Hans-Beerman/NodeOven/Photos/20200808_105303.jpg

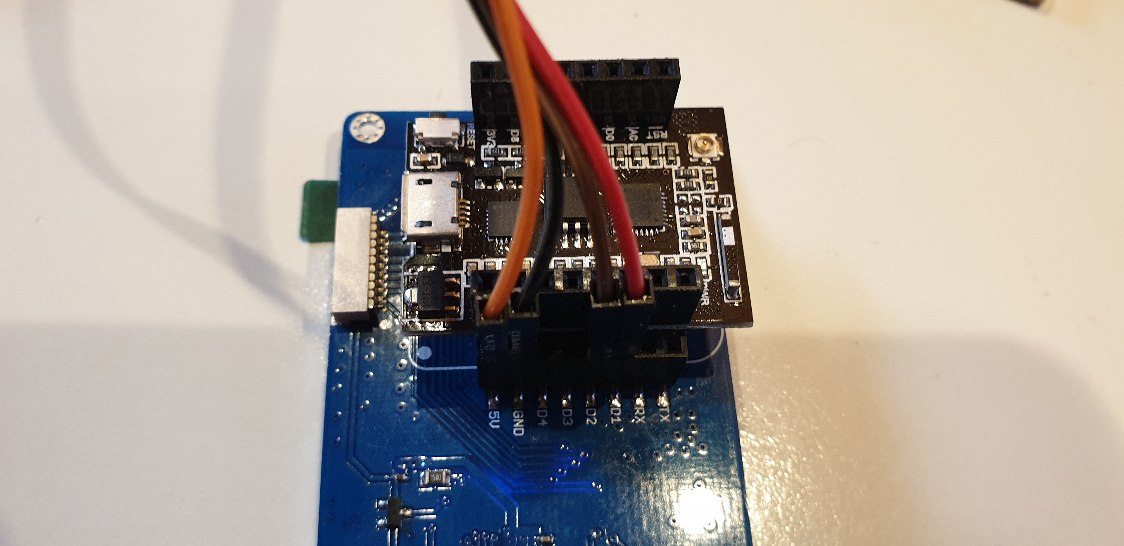
Photos/20200808_105303.jpg
