Hans-Beerman/NodeOven/Photos/20200808_163038.jpg

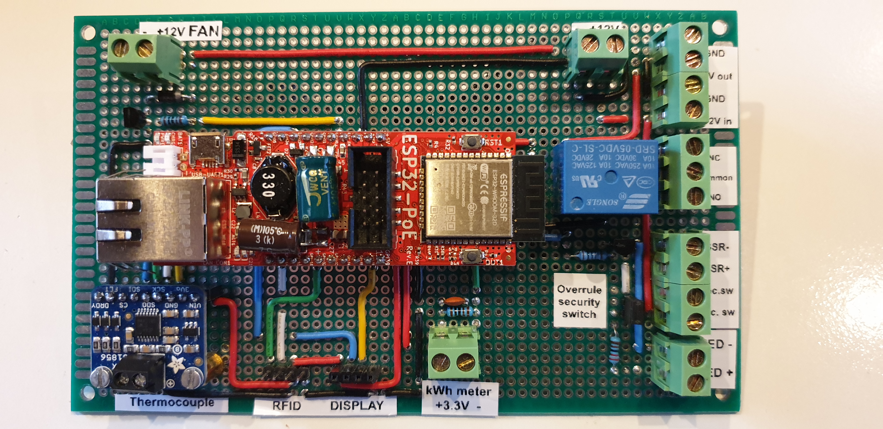
Photos/20200808_163038.jpg
