Hans-Beerman/NodeOven/Photos/20200809_112259.jpg

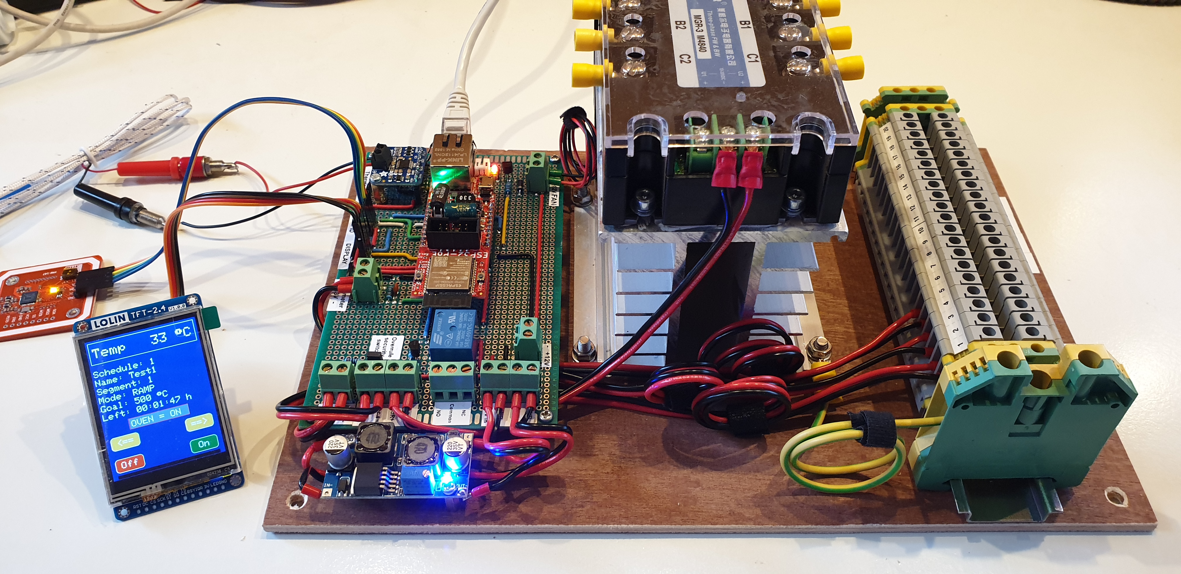
Photos/20200809_112259.jpg
