Hans-Beerman/NodeOven/Photos/20200809_112936.jpg

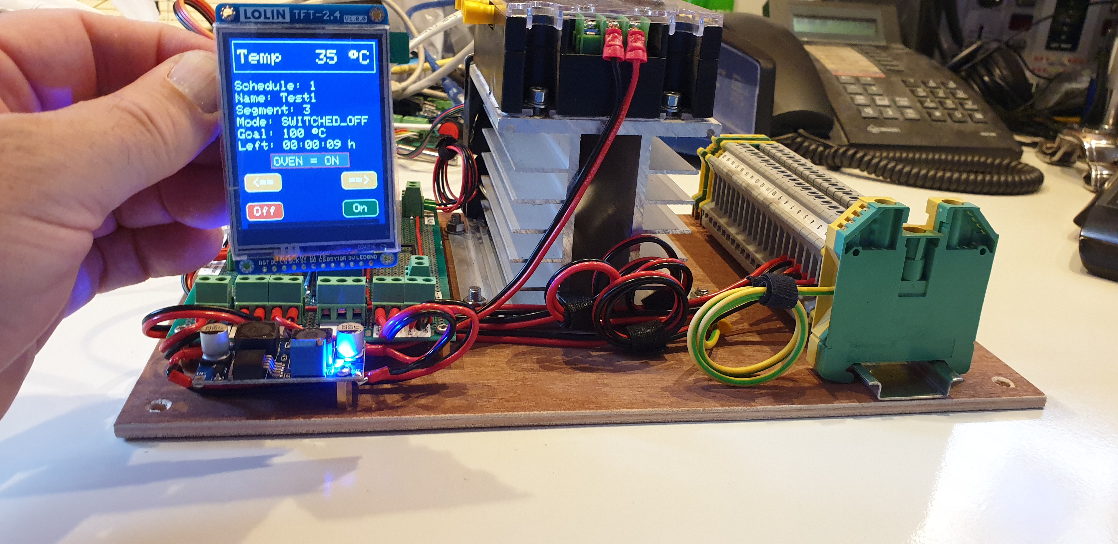
Photos/20200809_112936.jpg
