Hans-Beerman/NodeOven/Photos/20200809_221253.jpg

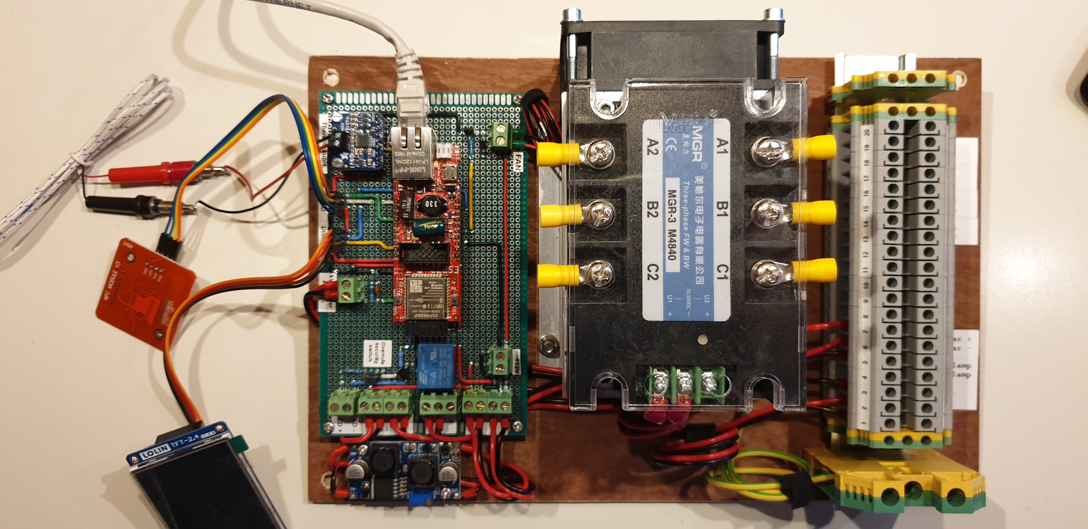
Photos/20200809_221253.jpg
